coelacant1/DeltaProtogen/Pictures/BottomLayer.png

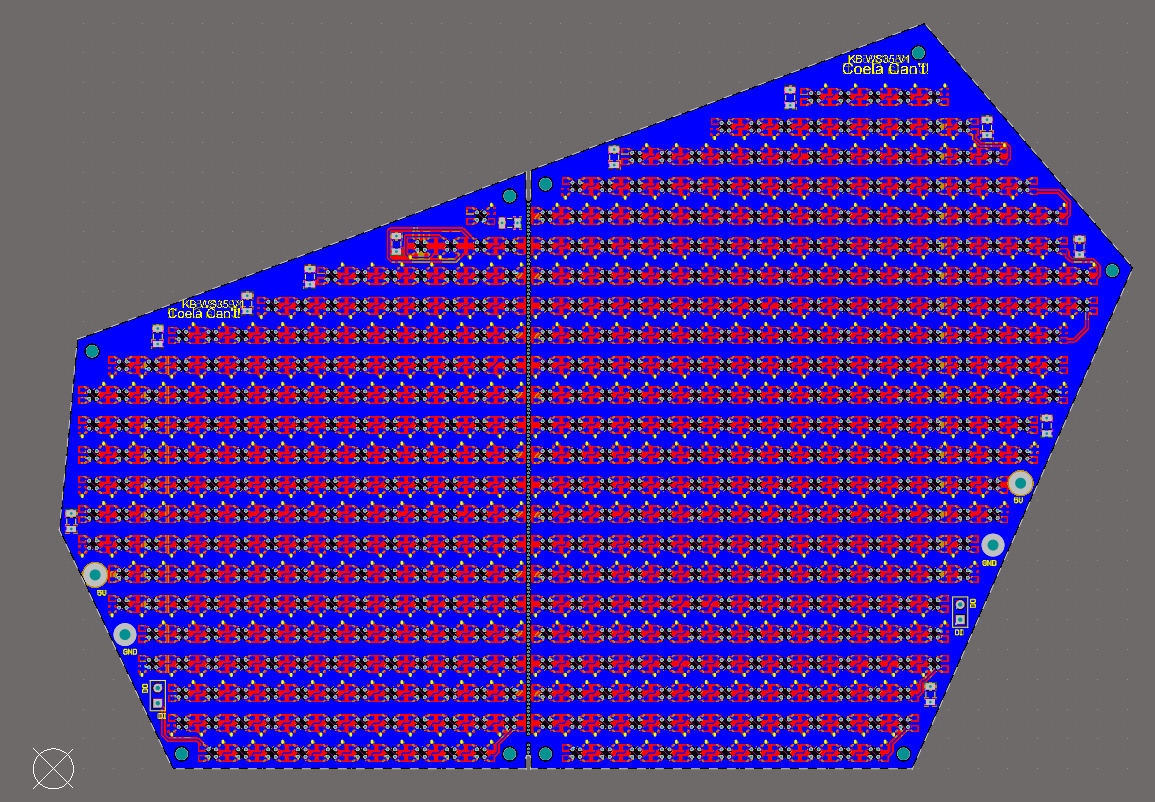
Pictures/BottomLayer.png
