coelacant1/DeltaProtogen/Pictures/CoelaProtoSmoothV1_P3Back.png

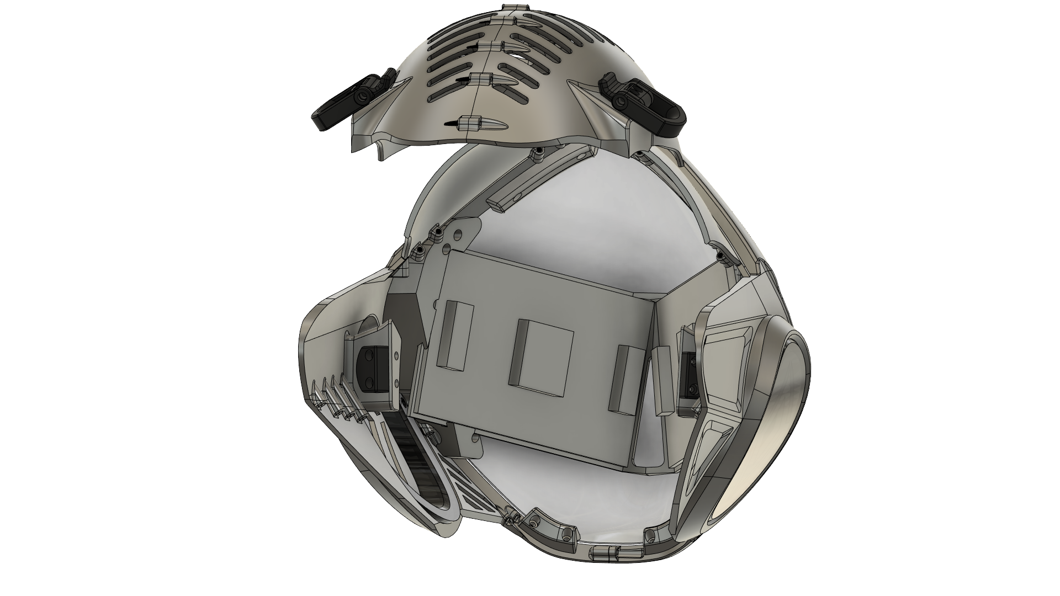
Pictures/CoelaProtoSmoothV1_P3Back.png
