coelacant1/DeltaProtogen/Pictures/CoelaProtoSmoothV1_WS35 P3.png

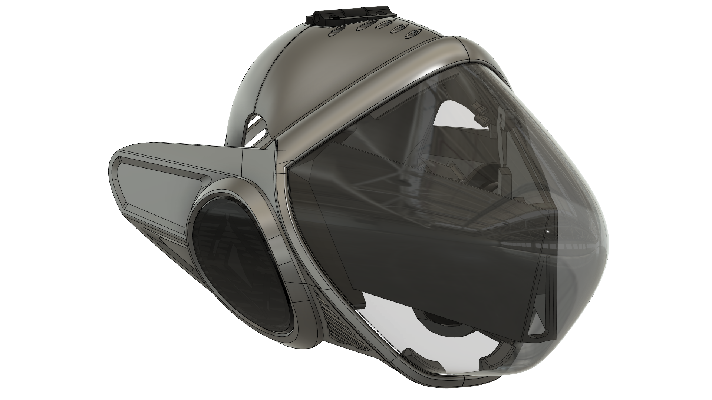
Pictures/CoelaProtoSmoothV1_WS35 P3.png
