coelacant1/DeltaProtogen/Pictures/CoelaProtoSmoothV1_WS35Back.png

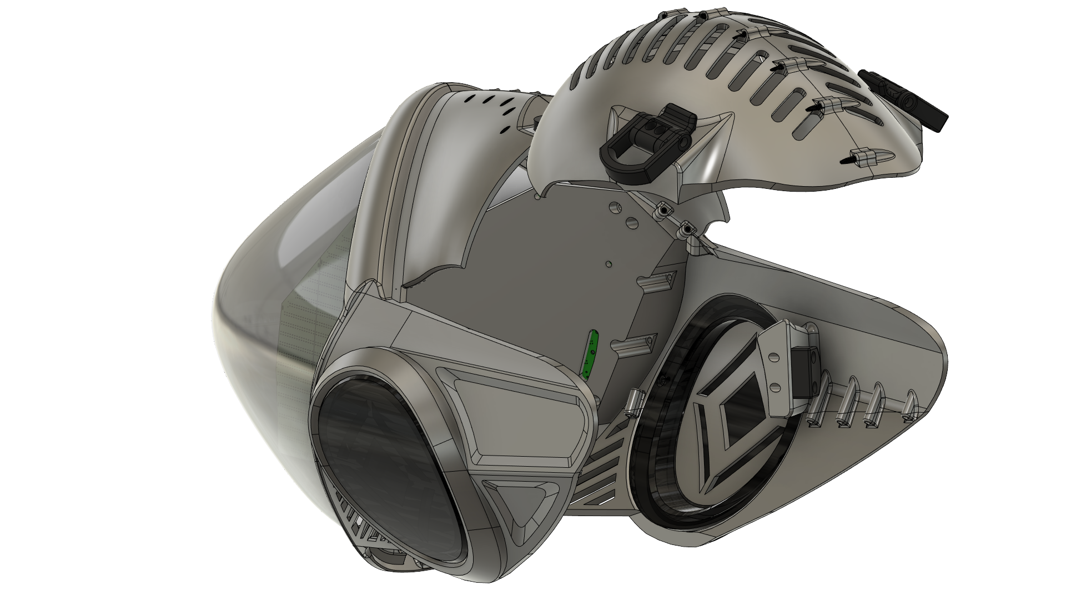
Pictures/CoelaProtoSmoothV1_WS35Back.png
