coelacant1/DeltaProtogen/Pictures/Delta Protogen V1.png

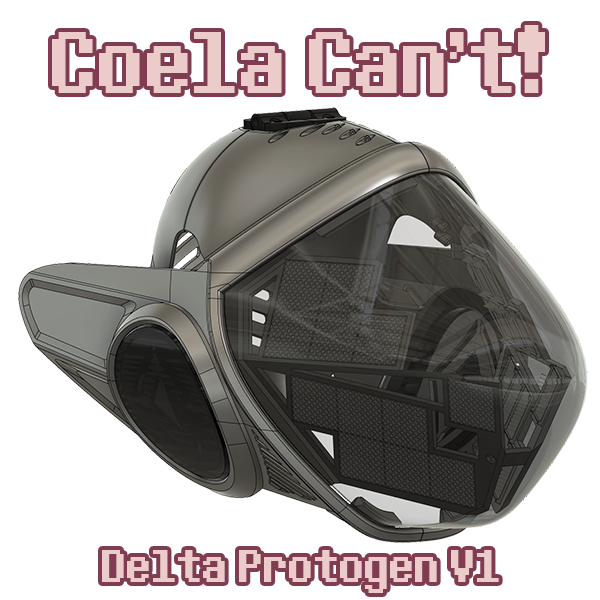
Pictures/Delta Protogen V1.png
