coelacant1/DeltaProtogen/Pictures/LED.png

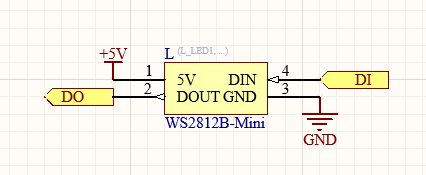
Pictures/LED.png
