coelacant1/DeltaProtogen/Pictures/SignalLayer2.png

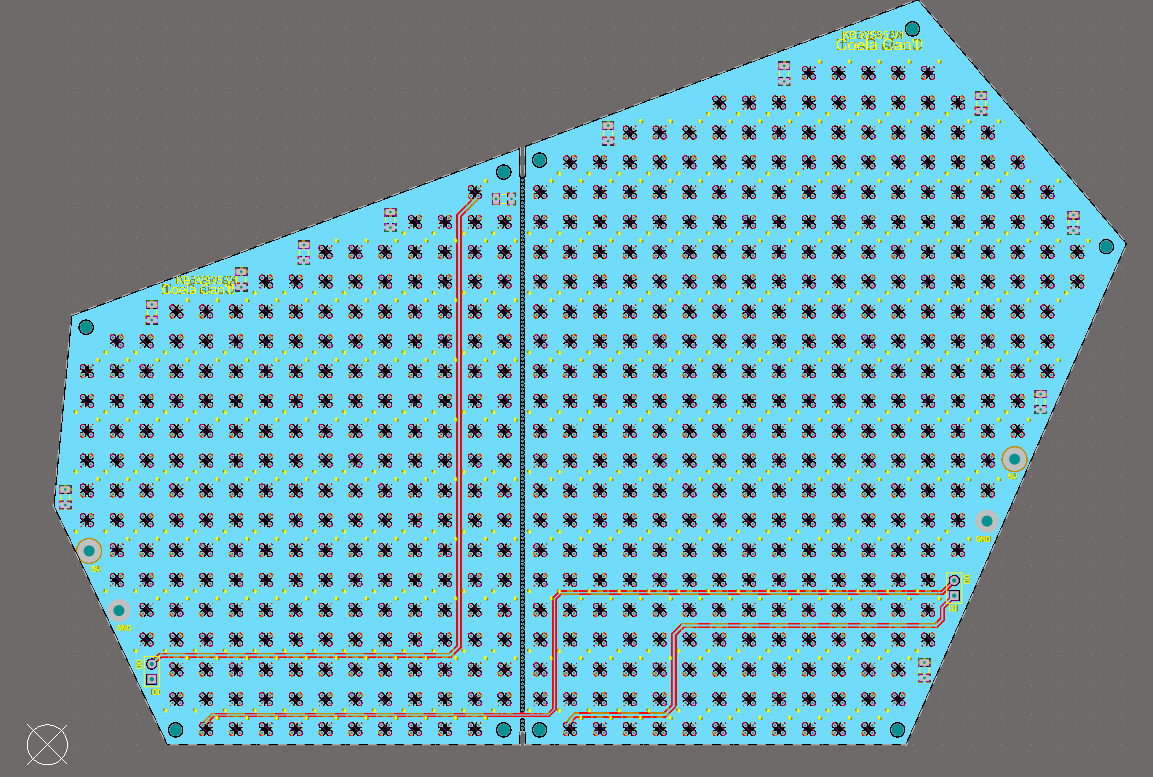
Pictures/SignalLayer2.png
