coelacant1/DeltaProtogen/Pictures/TopCopper.png

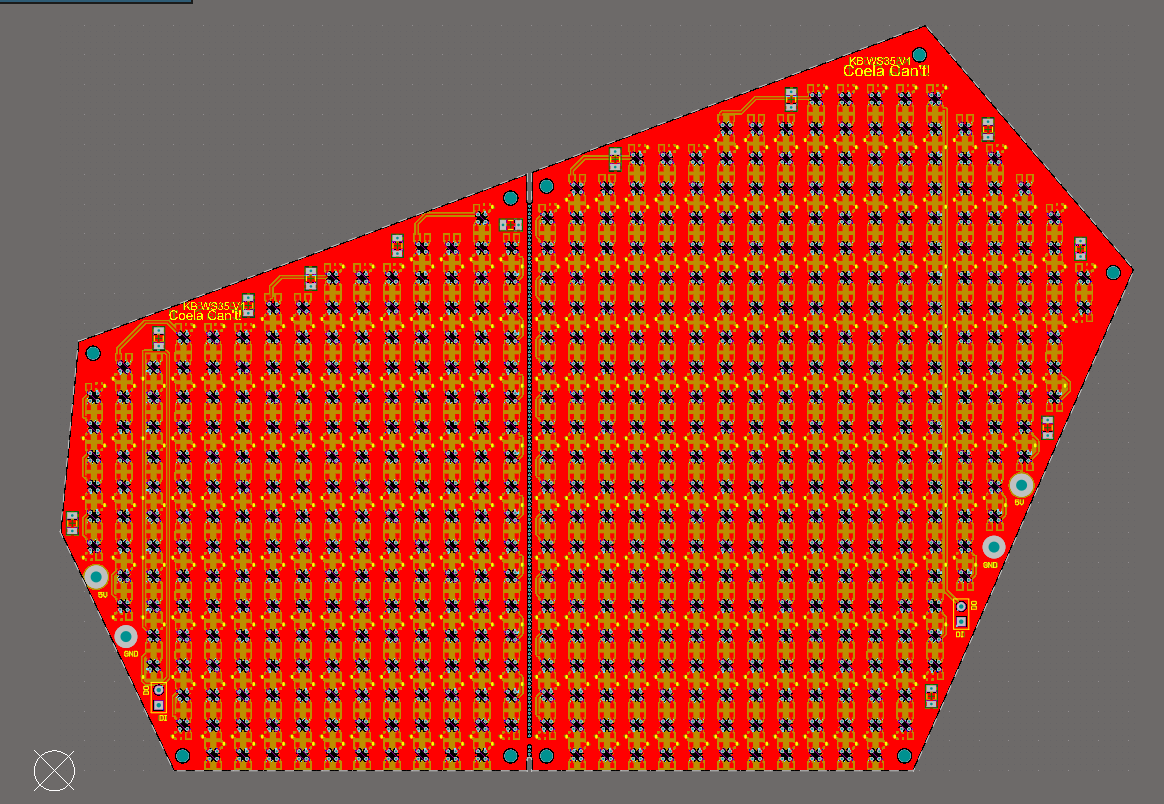
Pictures/TopCopper.png
