coelacant1/DeltaProtogen/LED Mount P3 HUB75/P3LeftMount_V1-0.stl

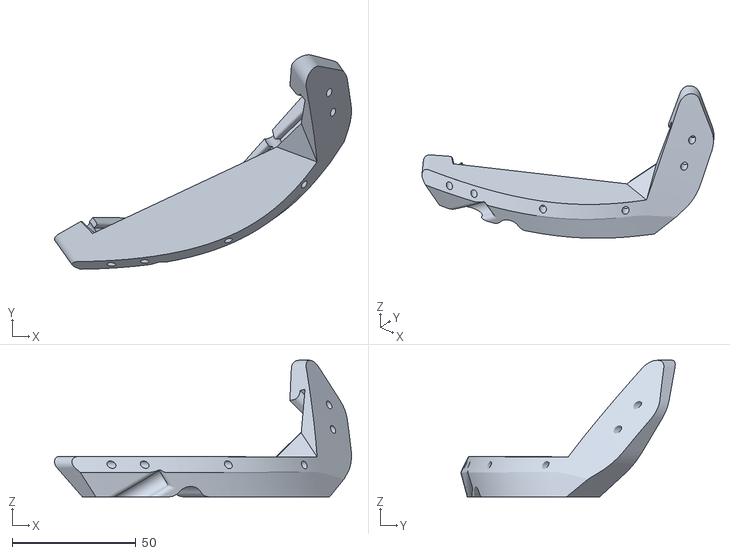
[picture p29: CAD file, 2023-06-26]
LED Mount P3 HUB75/P3LeftMount_V1-0.stl
120.0 x 86.7 x 55.2
