coelacant1/DeltaProtogen/Side Displays/LeftPuck_V1-0.stl

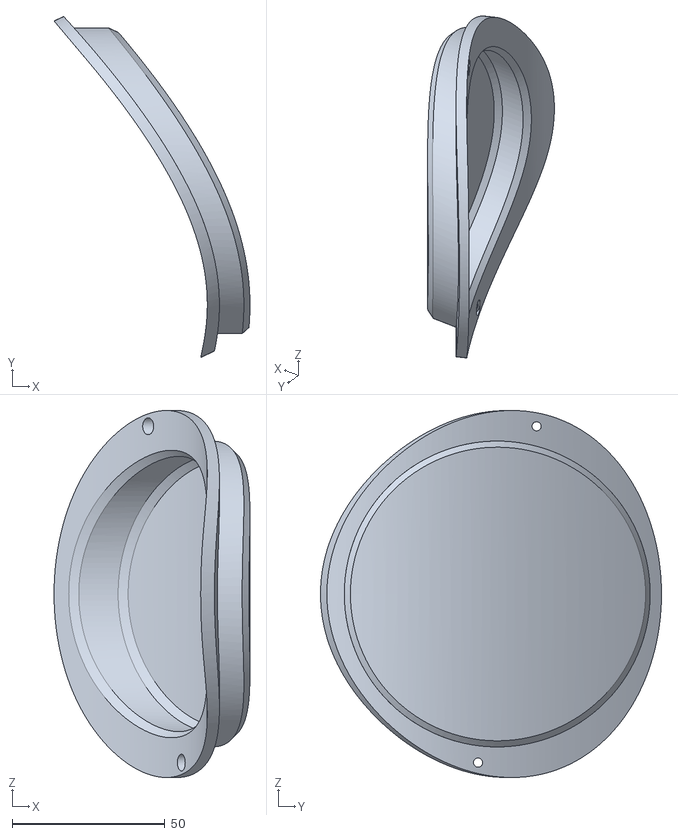
[picture p30: CAD file, 2023-06-26]
Side Displays/LeftPuck_V1-0.stl
64.1 x 111.5 x 120.0
