coelacant1/DeltaProtogen/Visor Mounts/VisorSupportBottomCover.stl

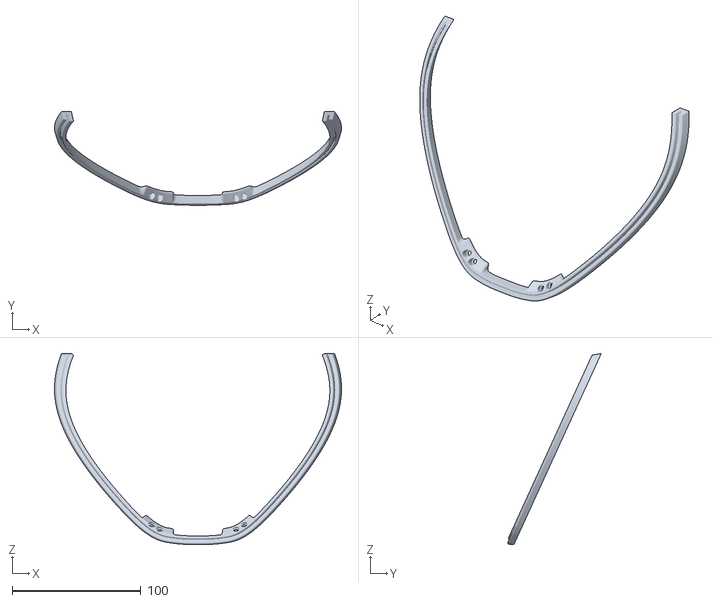
[picture p31: CAD file, 2024-06-24]
Visor Mounts/VisorSupportBottomCover.stl
222.9 x 72.7 x 148.4
