coelacant1/DeltaProtogen/Visor/BuckBotLeft_V3-0.stl

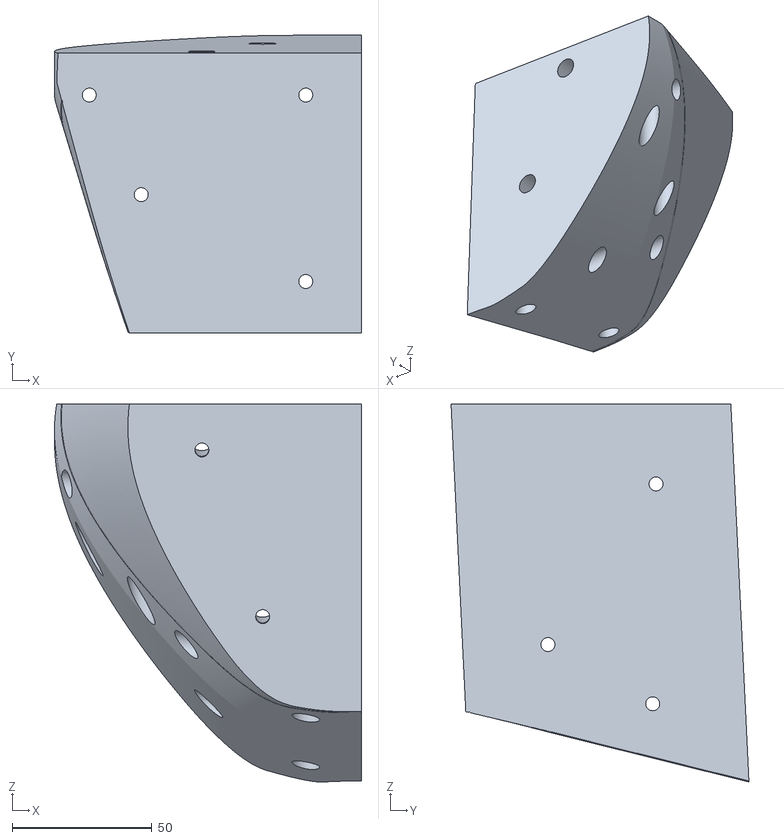
[picture p32: CAD file, 2023-06-26]
Visor/BuckBotLeft_V3-0.stl
109.8 x 106.6 x 135.2
