coelacant1/DeltaProtogen/Frame/RightBottom_V1-0.stl

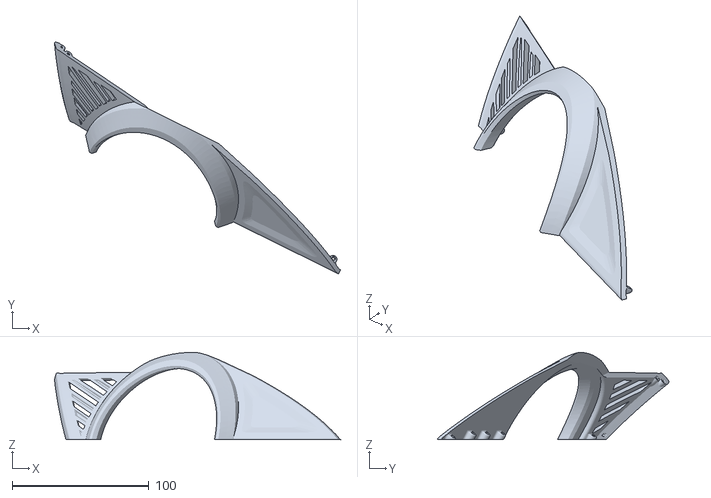
[picture p33: CAD file, 2023-06-26]
Frame/RightBottom_V1-0.stl
209.3 x 169.7 x 63.8
