coelacant1/DeltaProtogen/Latch/LatchOuterRotateWider_V1-0.stl

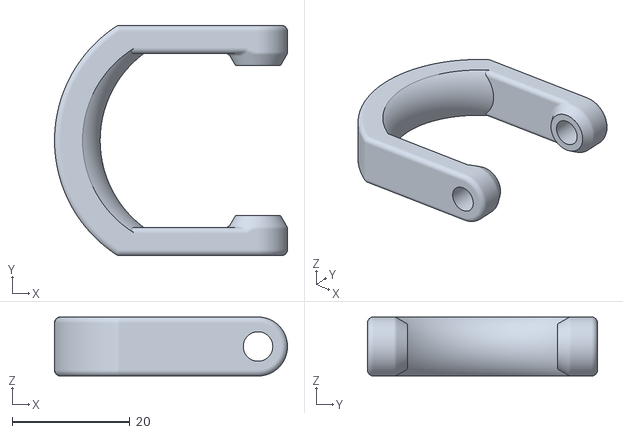
[picture p34: CAD file, 2023-06-26]
Latch/LatchOuterRotateWider_V1-0.stl
39.5 x 39.0 x 10.0
