coelacant1/DeltaProtogen/LED Mount KS W35/KSWS35_Right_V1-0.stl

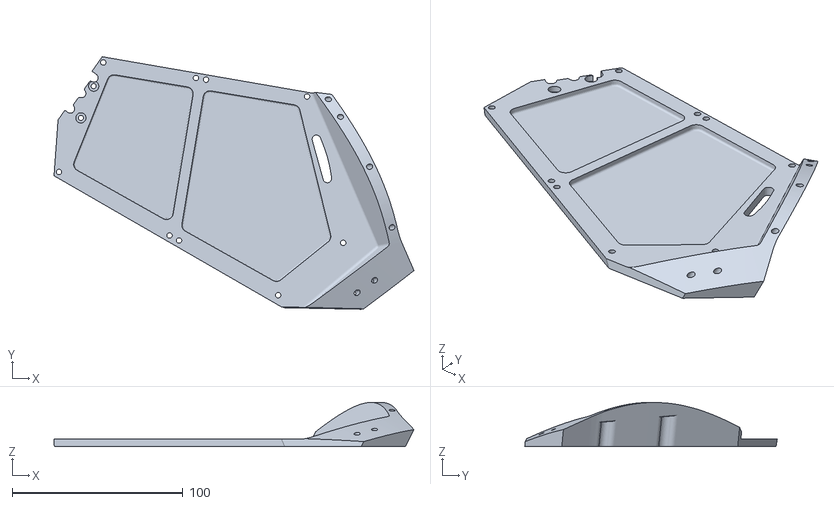
[picture p35: CAD file, 2023-06-26]
LED Mount KS W35/KSWS35_Right_V1-0.stl
210.8 x 147.9 x 25.8
