coelacant1/DeltaProtogen/LED Mount P3 HUB75/P3RightMount_V1-0.stl

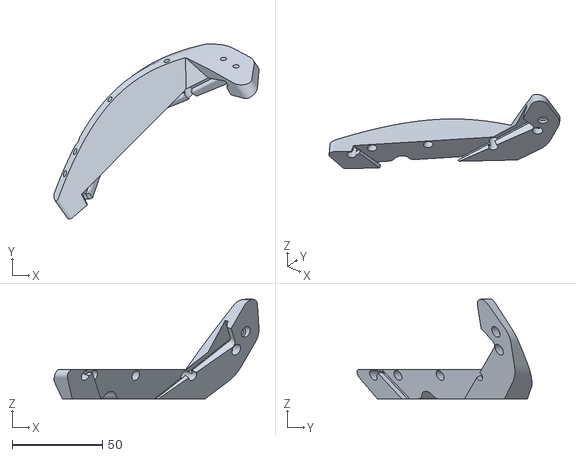
[picture p36: CAD file, 2023-06-26]
LED Mount P3 HUB75/P3RightMount_V1-0.stl
113.7 x 97.0 x 55.2
