coelacant1/DeltaProtogen/Side Displays/RightPuckInner_V1-0.stl

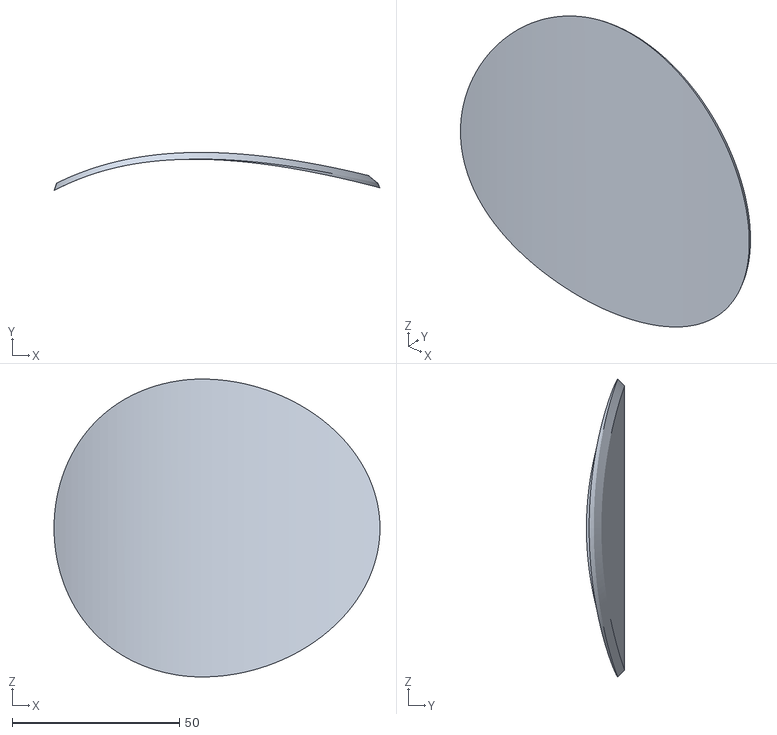
[picture p37: CAD file, 2023-06-26]
Side Displays/RightPuckInner_V1-0.stl
97.4 x 11.4 x 89.0
