coelacant1/DeltaProtogen/Visor Mounts/VisorSupportBottom.stl

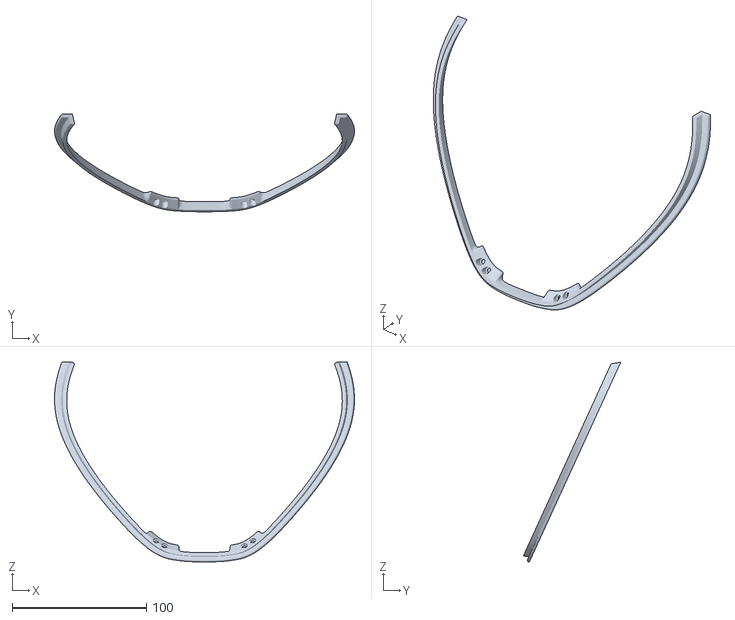
[picture p38: CAD file, 2023-08-20]
Visor Mounts/VisorSupportBottom.stl
223.2 x 72.6 x 148.6
