coelacant1/DeltaProtogen/Frame/RightHead_V1-0.stl

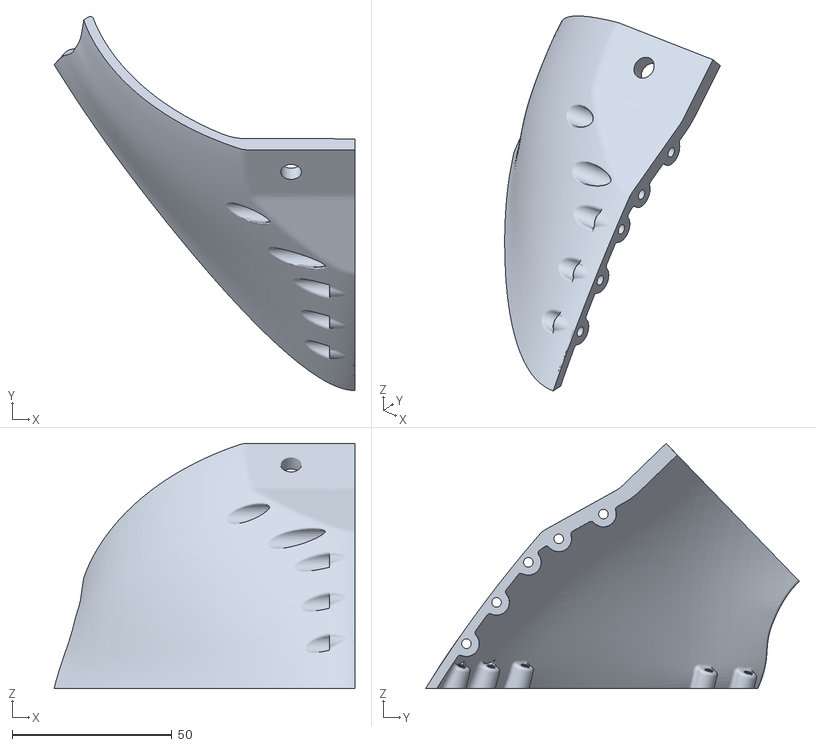
[picture p40: CAD file, 2023-06-26]
Frame/RightHead_V1-0.stl
94.1 x 117.0 x 76.7
