coelacant1/DeltaProtogen/LED Mount MAX7219/MAX7219BotRight_V1-0.stl

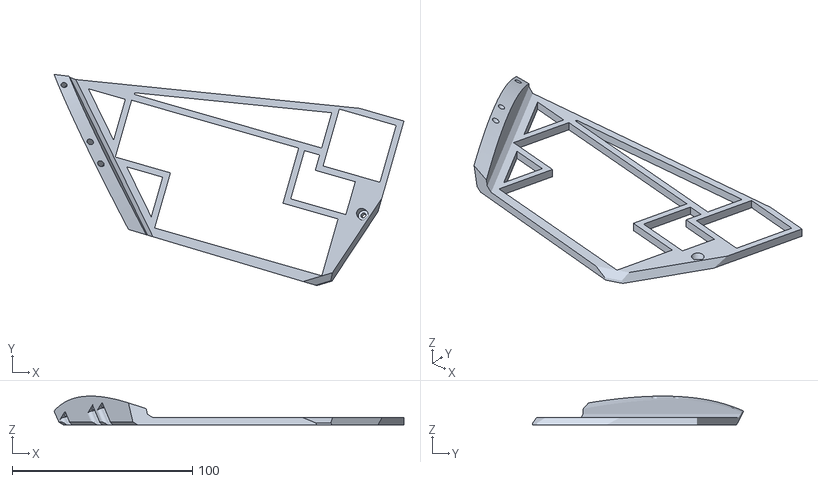
[picture p42: CAD file, 2023-06-26]
LED Mount MAX7219/MAX7219BotRight_V1-0.stl
194.1 x 117.2 x 16.0
