coelacant1/DeltaProtogen/Visor Mounts/VisorSupportTop.stl

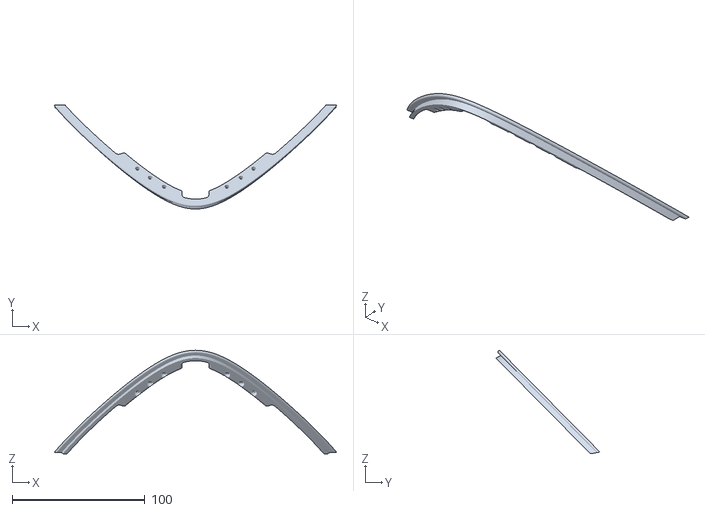
[picture p43: CAD file, 2023-08-20]
Visor Mounts/VisorSupportTop.stl
212.3 x 78.3 x 77.9
