coelacant1/DeltaProtogen/Visor/BuckTopLeft_V3-0.stl

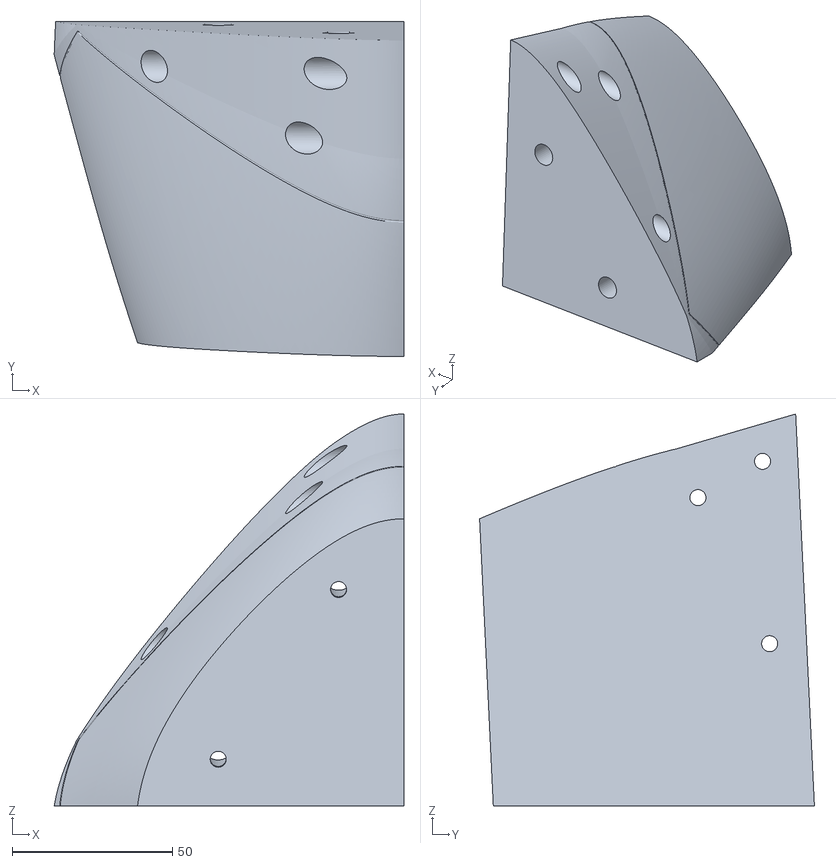
[picture p44: CAD file, 2023-06-26]
Visor/BuckTopLeft_V3-0.stl
109.0 x 104.4 x 122.2
