coelacant1/DeltaProtogen/Frame/LeftBackMid_V1-0.stl

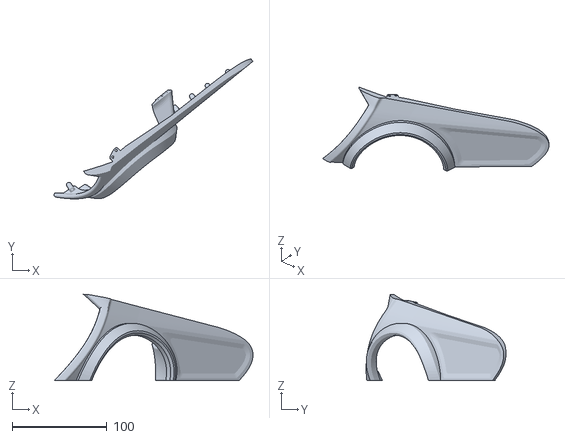
[picture p45: CAD file, 2023-06-26]
Frame/LeftBackMid_V1-0.stl
209.7 x 147.3 x 91.1
