coelacant1/DeltaProtogen/Latch/LatchInnerRotate_V1-0.stl

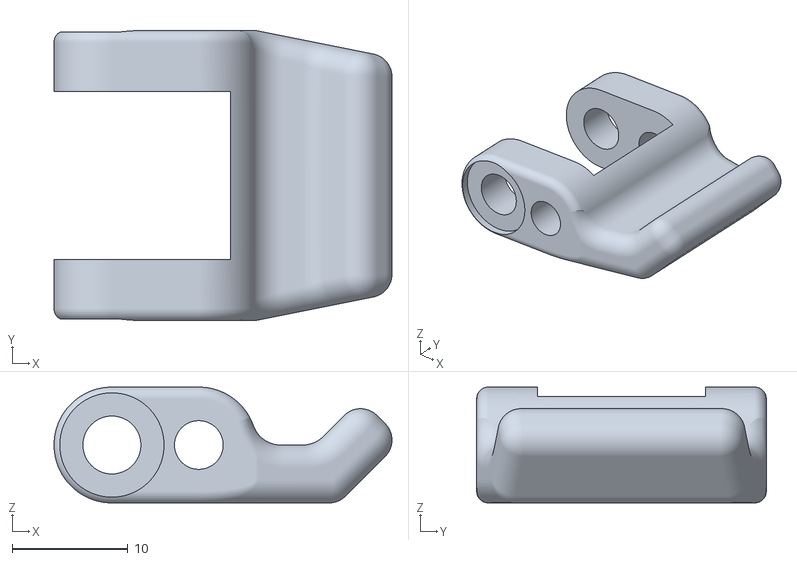
[picture p46: CAD file, 2023-06-26]
Latch/LatchInnerRotate_V1-0.stl
29.2 x 25.0 x 10.0
