coelacant1/DeltaProtogen/LED Mount MAX7219/MAX7219Connector_V1-0.stl

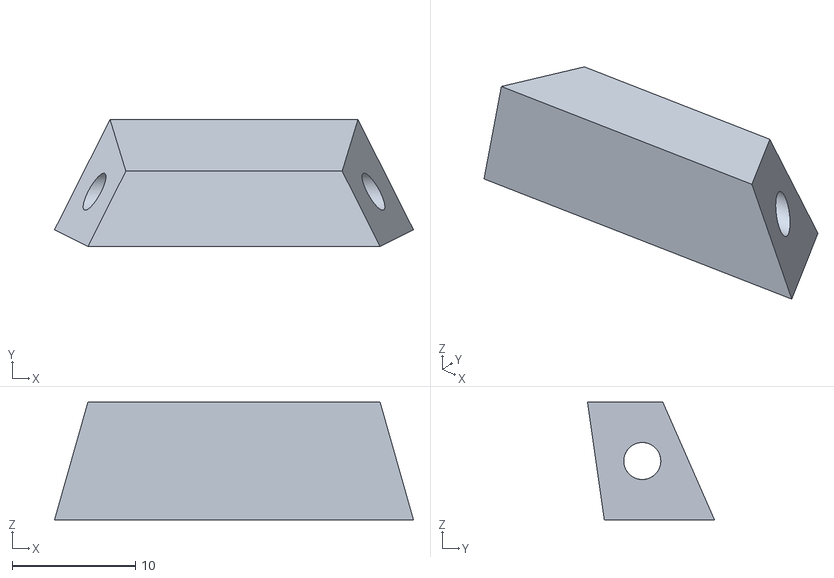
[picture p47: CAD file, 2023-06-26]
LED Mount MAX7219/MAX7219Connector_V1-0.stl
29.1 x 10.3 x 9.53
