coelacant1/DeltaProtogen/Visor Mounts/BottomLeftInner_V1-1.stl

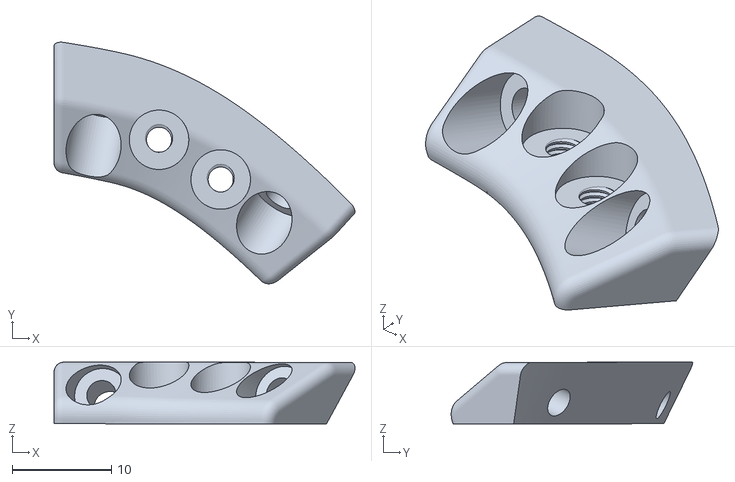
[picture p48: CAD file, 2023-06-26]
Visor Mounts/BottomLeftInner_V1-1.stl
30.4 x 24.4 x 6.23
