coelacant1/DeltaProtogen/Visor/Buck_V2-0.stl

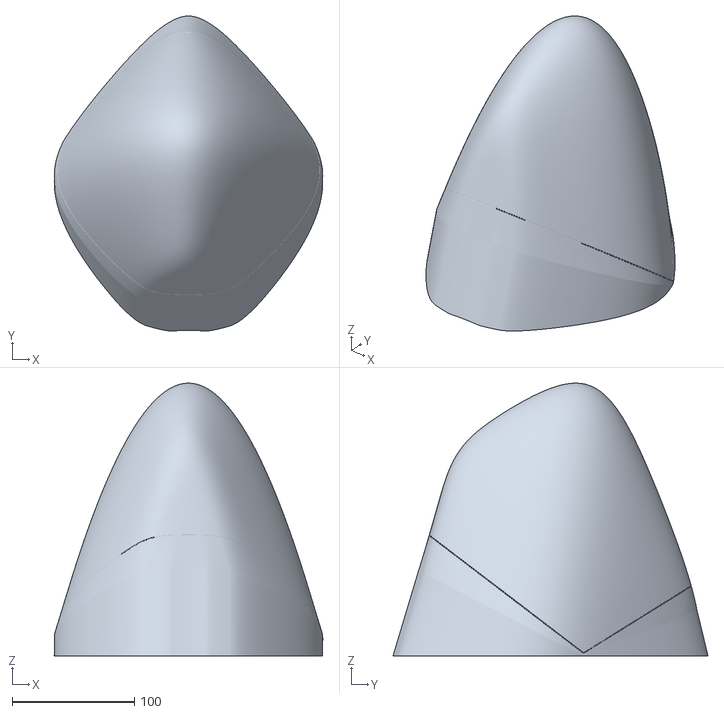
[picture p49: CAD file, 2023-06-26]
Visor/Buck_V2-0.stl
219.7 x 257.7 x 223.1
