coelacant1/DeltaProtogen/Frame/TopRightForehead_V1-0.stl

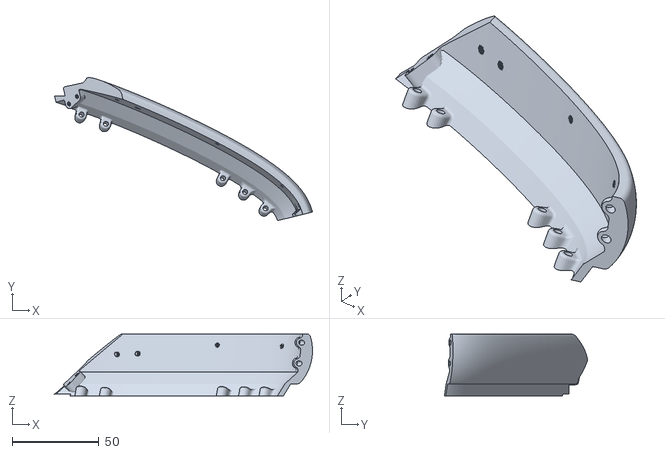
[picture p50: CAD file, 2023-06-26]
Frame/TopRightForehead_V1-0.stl
148.4 x 82.4 x 35.7
