coelacant1/DeltaProtogen/Visor Mounts/TopLeftInner_V1-1.stl

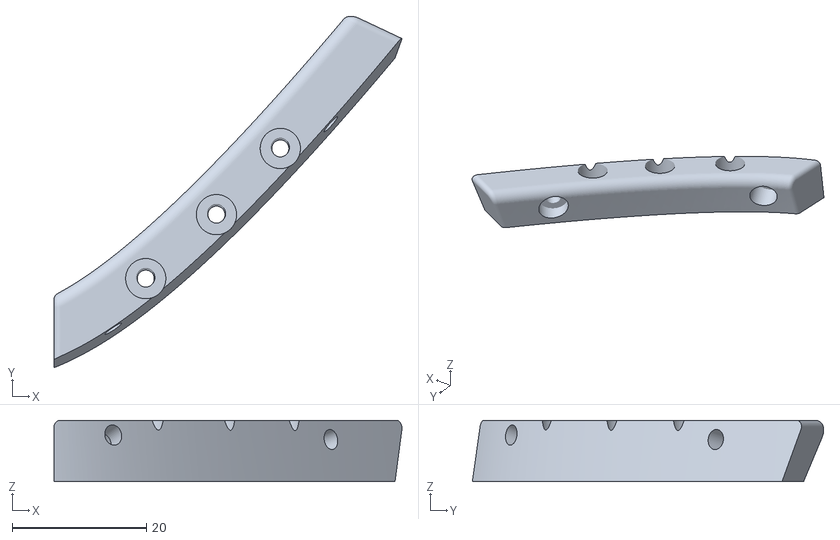
[picture p51: CAD file, 2023-06-26]
Visor Mounts/TopLeftInner_V1-1.stl
51.8 x 52.3 x 9.16
