coelacant1/DeltaProtogen/Frame/LeftBottom_V1-0.stl

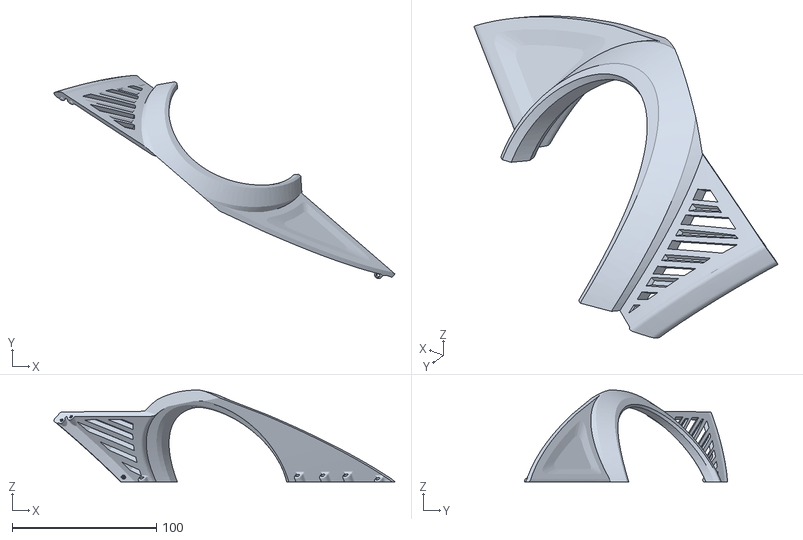
[picture p53: CAD file, 2023-06-26]
Frame/LeftBottom_V1-0.stl
236.8 x 141.2 x 63.8
