coelacant1/DeltaProtogen/Frame/RightBackMid_V1-0.stl

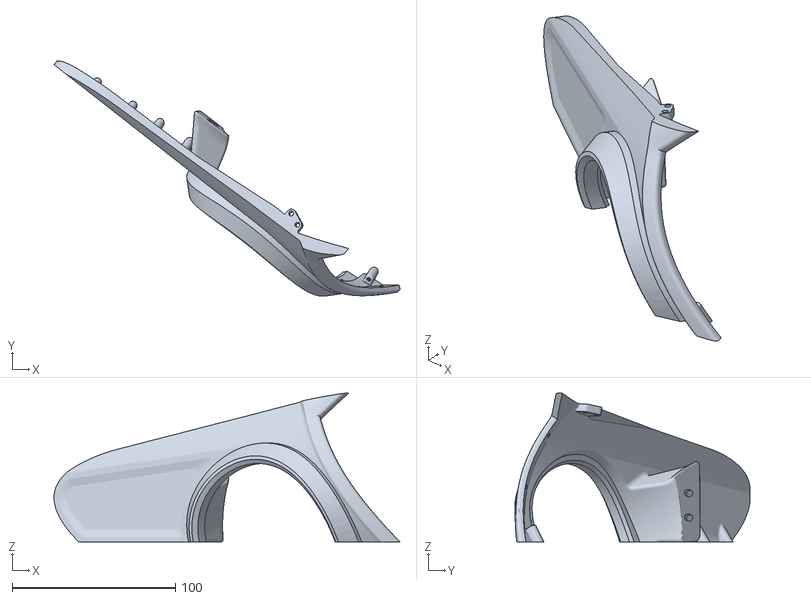
[picture p54: CAD file, 2023-06-26]
Frame/RightBackMid_V1-0.stl
212.1 x 144.3 x 91.1
