coelacant1/DeltaProtogen/Frame/RightJaw_V1-0.stl

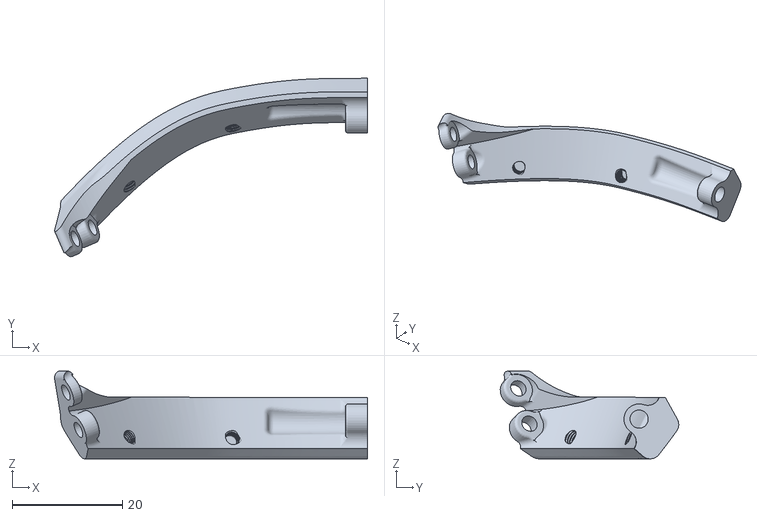
[picture p55: CAD file, 2023-06-26]
Frame/RightJaw_V1-0.stl
56.7 x 32.4 x 15.9
