coelacant1/DeltaProtogen/Frame/RightBackHelmet_V1-0.stl

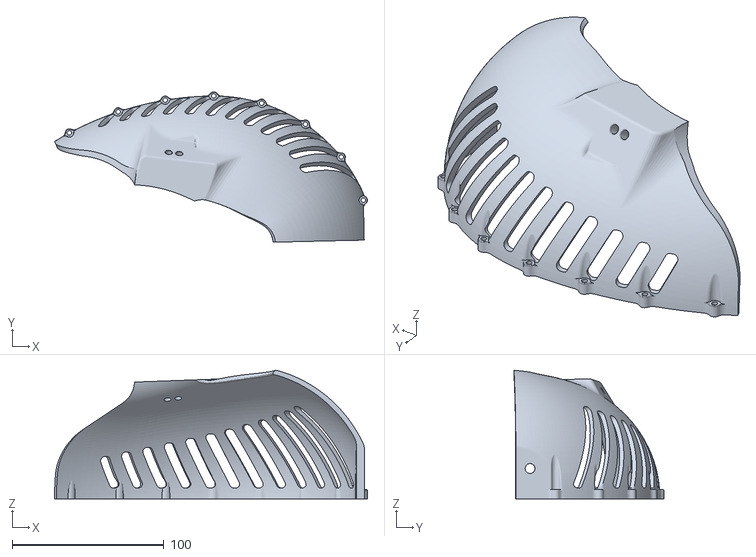
[picture p56: CAD file, 2023-06-26]
Frame/RightBackHelmet_V1-0.stl
206.4 x 99.2 x 84.9
