coelacant1/DeltaProtogen/Frame/LeftJaw_V1-0.stl

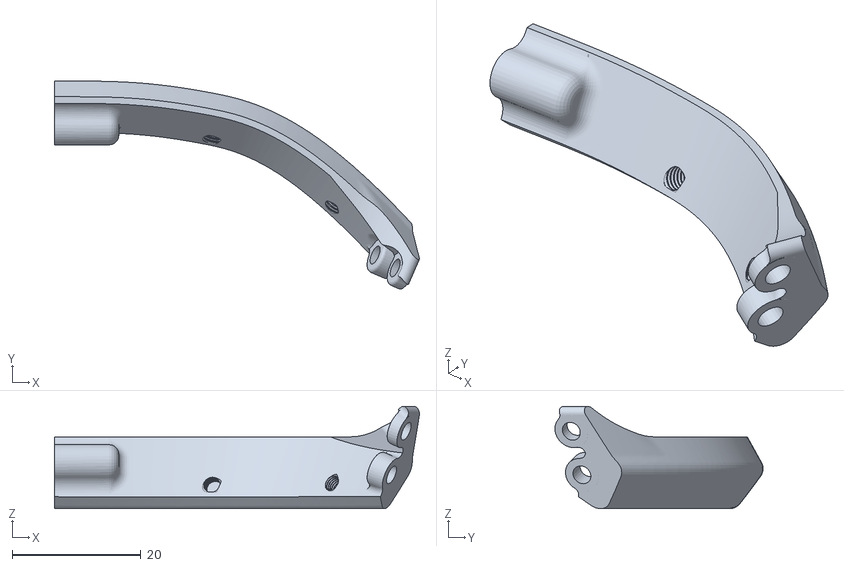
[picture p57: CAD file, 2023-06-26]
Frame/LeftJaw_V1-0.stl
56.7 x 32.4 x 15.9
