coelacant1/DeltaProtogen/Frame/TopLeftForehead_V1-0.stl

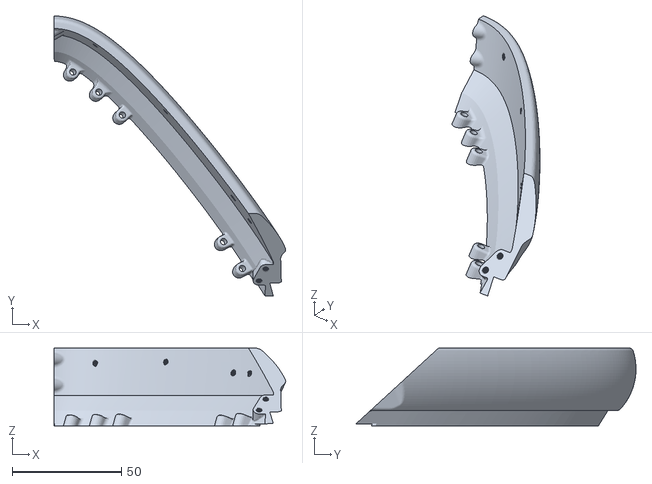
[picture p58: CAD file, 2023-06-26]
Frame/TopLeftForehead_V1-0.stl
106.0 x 128.2 x 35.7
