coelacant1/DeltaProtogen/LED Board References/ProtoTracerWiringDiagram.png

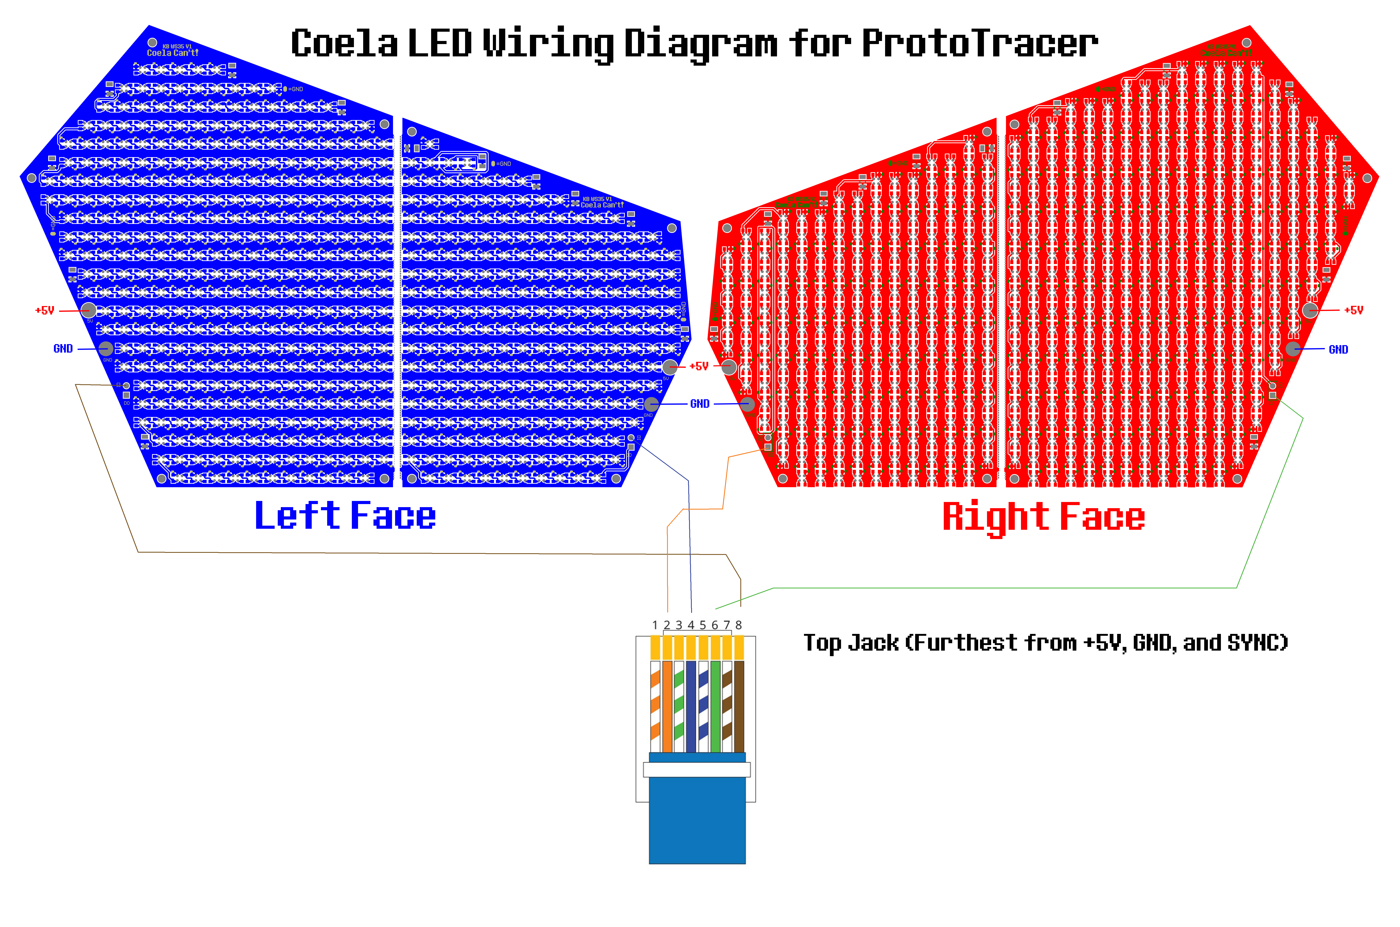
LED Board References/ProtoTracerWiringDiagram.png
